NURobotics/nurc-workshop/res/capacitor.png

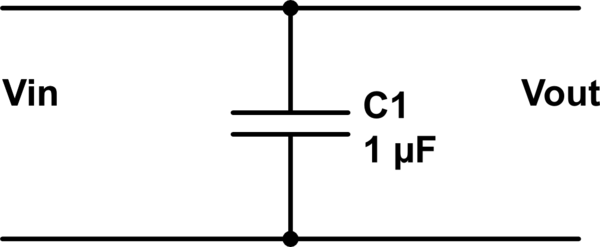
res/capacitor.png
