NURobotics/nurc-workshop/res/compilation.png

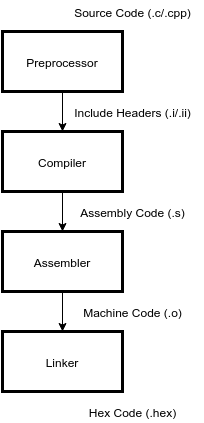
res/compilation.png
