NURobotics/nurc-workshop/res/darwin-op.jpg

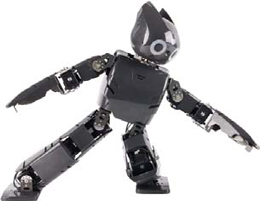
res/darwin-op.jpg
