NURobotics/nurc-workshop/res/led-vi.jpg

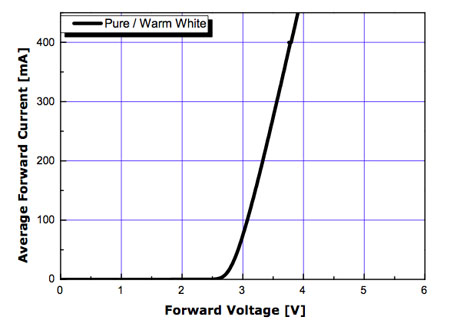
res/led-vi.jpg
