NURobotics/nurc-workshop/res/vreg.png

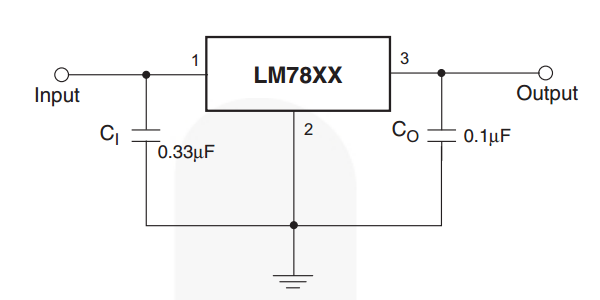
res/vreg.png
