NURobotics/nurc-workshop/eagle-cad/line_follower.sch

## EAGLE design eagle-cad/line_follower.sch (2015-10-17)

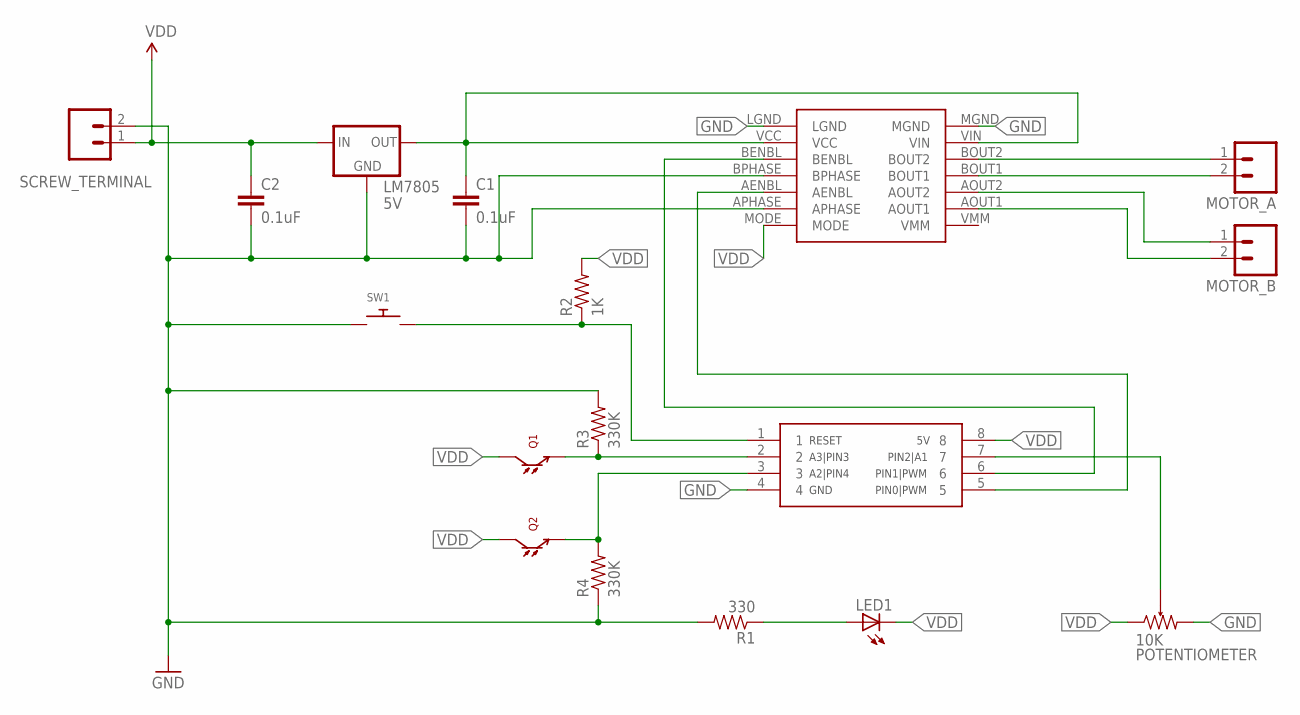
[picture p24: schematic line_follower.sch]

Parts:
10K: POTENTIOMETER; 0603-ARV
ATTINY85: ATTINY85; ATTINY_DIP
C1, C2: 0.1uF; CAP-PTH-SMALLEZ
DRV8835: POLOLU_MOTOR_DRV8835THROUGHHOLE; POLOLU_MOTOR_DRV_DRV8835
LED1: LED5MM
LM7805: 5V; 78XXS
MOTOR_A: M02PTH; 1X02
MOTOR_B: M02PTH; 1X02
Q1, Q2: LTR-301
R1: 330; AXIAL-0.3EZ
R2: 1K; AXIAL-0.3EZ
R3, R4: 330K; AXIAL-0.3EZ
SCREW_TERMINAL: M02JST-PTH-VERT; JST-2-PTH-VERT
SW1: SWITCH_PUSHBUTTONEVQ-PE; TACT_PANA-EVQ

Connections:
GND: 10K.2, ATTINY85.4, C1.2, C2.2, DRV8835.APHASE, DRV8835.BPHASE, DRV8835.LGND, DRV8835.MGND, LM7805.GND, R1.P$2 (2), R3.P$2 (2), R4.P$1 (1), SCREW_TERMINAL.2, SW1.P$1
unnamed: 10K.3, ATTINY85.7
unnamed: ATTINY85.1, R2.P$1 (1), SW1.P$2
unnamed: ATTINY85.3, Q2.E, R4.P$2 (2)
unnamed: ATTINY85.5, DRV8835.AENBL
unnamed: ATTINY85.6, DRV8835.BENBL
unnamed: LED1.A, R1.P$1 (1)
unnamed: DRV8835.AOUT1, MOTOR_B.2
unnamed: DRV8835.AOUT2, MOTOR_B.1
unnamed: DRV8835.BOUT1, MOTOR_A.2
unnamed: DRV8835.BOUT2, MOTOR_A.1
unnamed: ATTINY85.2, Q1.E, R3.P$1 (1)
VDD: 10K.1, ATTINY85.8, C1.1, C2.1, DRV8835.MODE, DRV8835.VCC, DRV8835.VIN, LED1.K (C), LM7805.IN, LM7805.OUT, Q1.C, Q2.C, R2.P$2 (2), SCREW_TERMINAL.1
