NURobotics/nurc-workshop/res/assembly.jpg

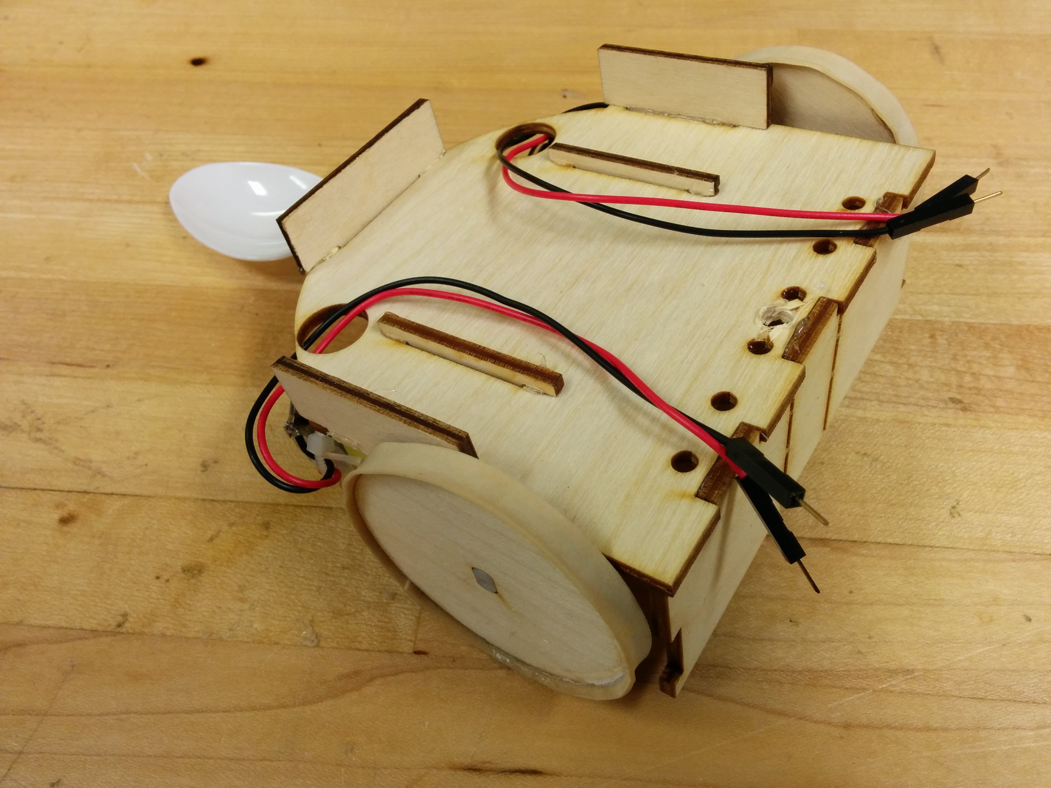
res/assembly.jpg
