NURobotics/nurc-workshop/res/assembly_1.jpg

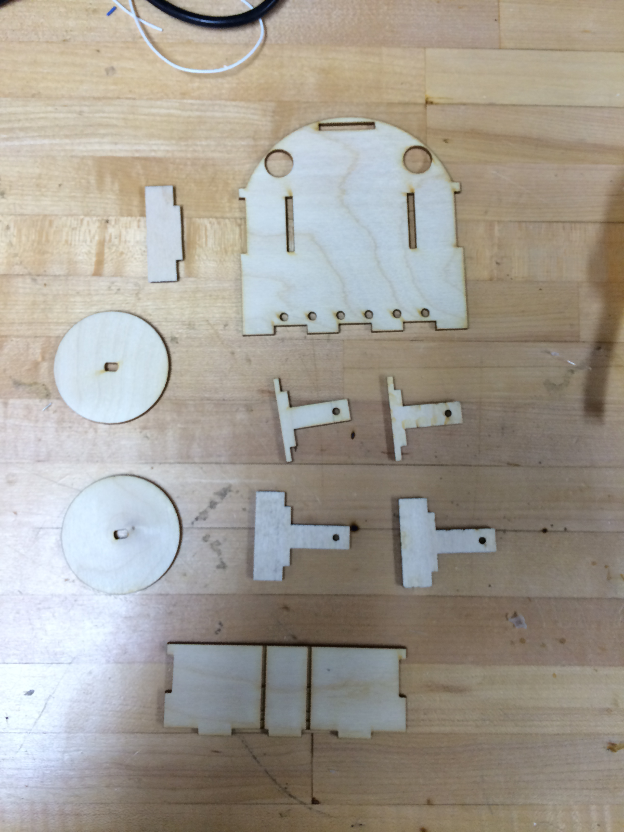
res/assembly_1.jpg
