NURobotics/nurc-workshop/res/assembly_2.jpg

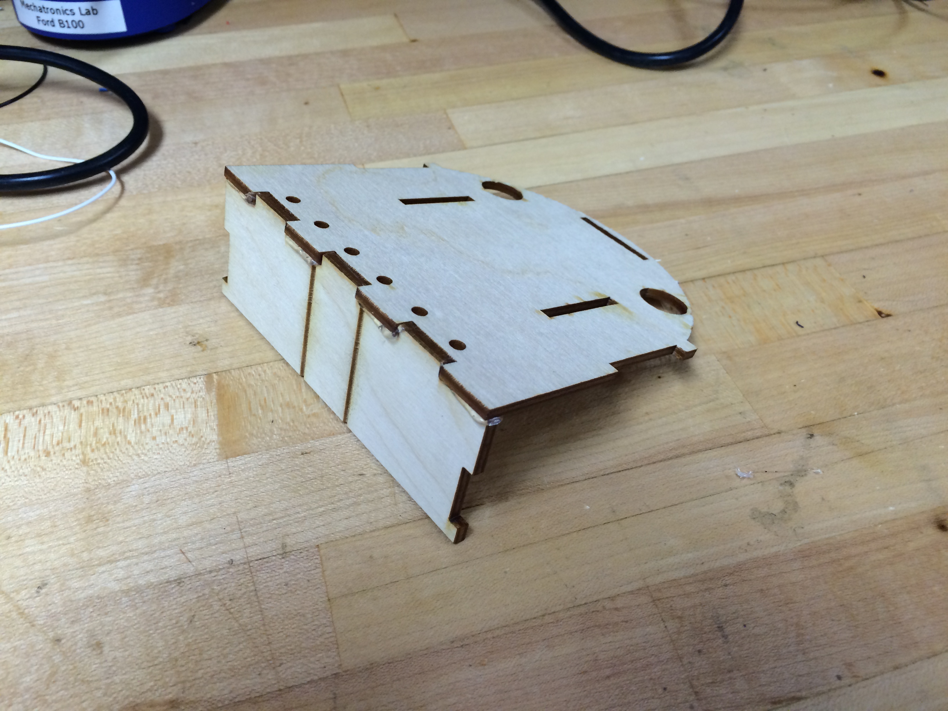
res/assembly_2.jpg
