NURobotics/nurc-workshop/res/assembly_4.jpg

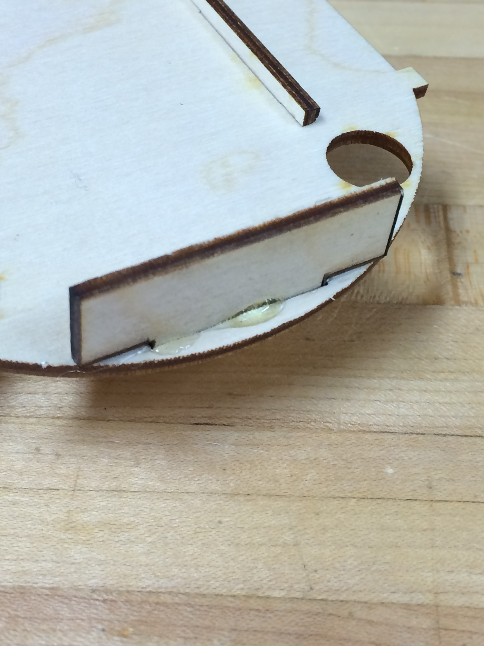
res/assembly_4.jpg
