NURobotics/nurc-workshop/res/assembly_7.jpg

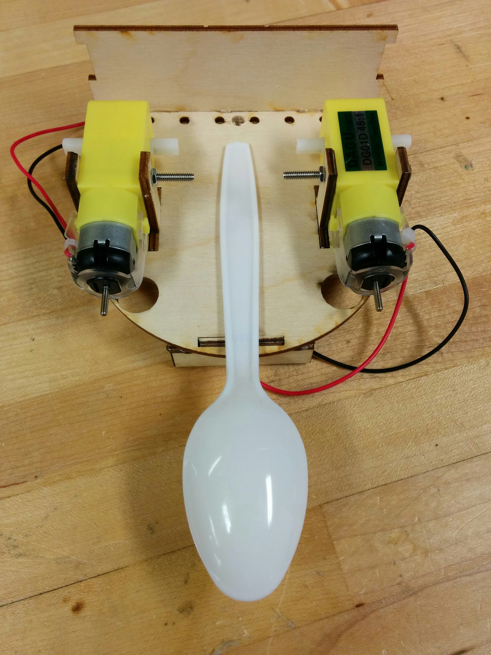
res/assembly_7.jpg
