NURobotics/nurc-workshop/res/assembly_8.jpg

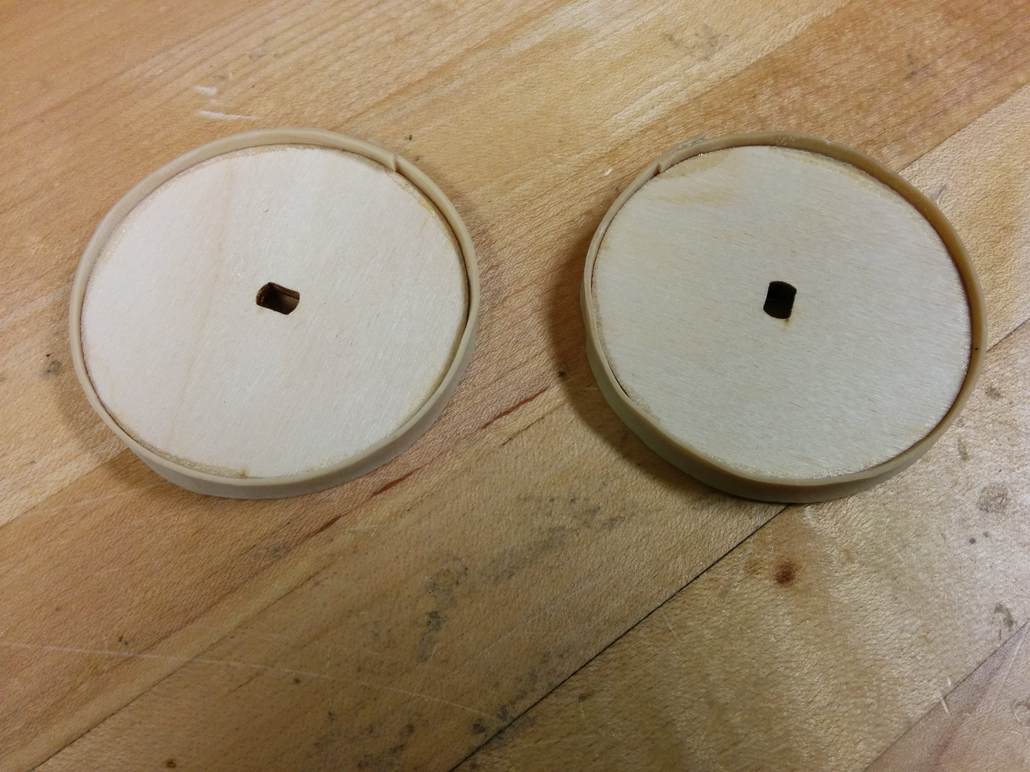
res/assembly_8.jpg
