NURobotics/nurc-workshop/res/solder_down.jpg

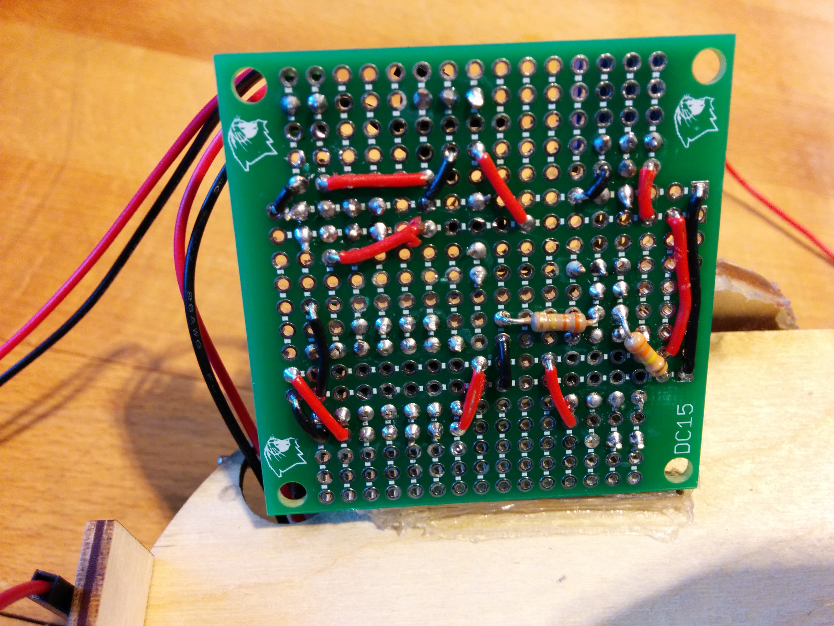
res/solder_down.jpg
